joncox123/MotoButtons/ConstructionGuide/Photos/Dremel_PCB_Posts.jpg

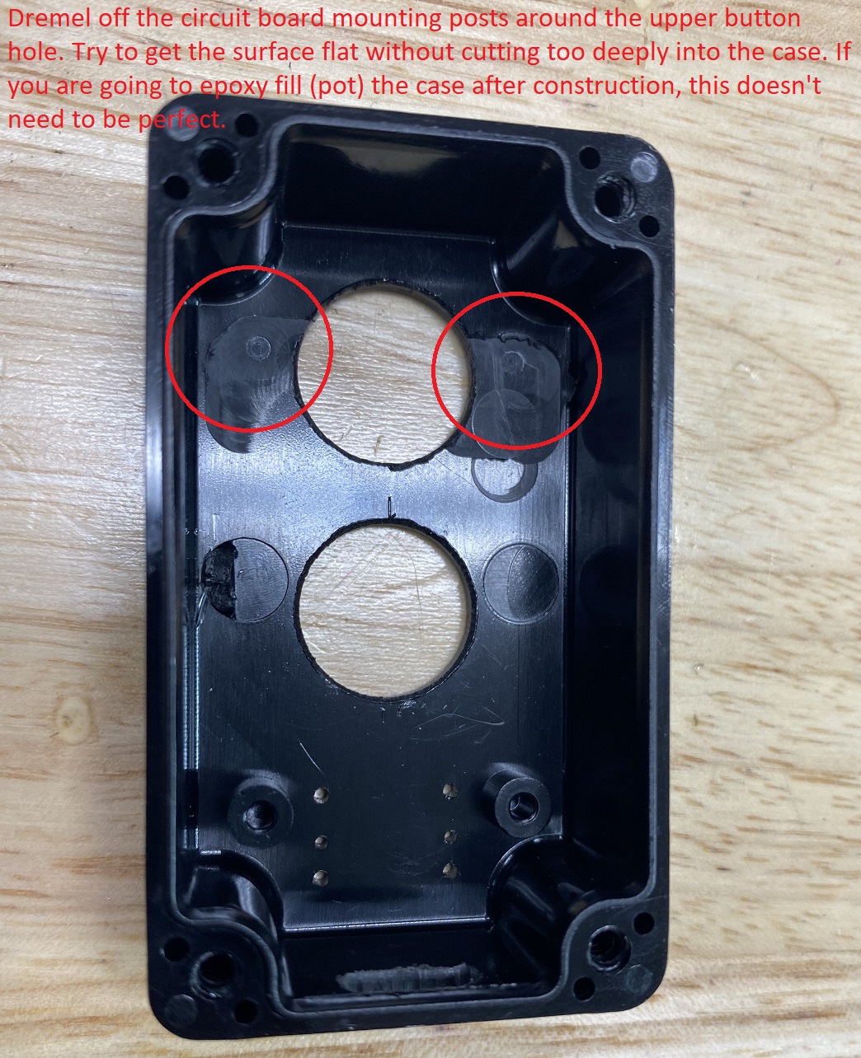
ConstructionGuide/Photos/Dremel_PCB_Posts.jpg
