joncox123/MotoButtons/ConstructionGuide/Photos/seeed-studio-xiao-nrf52840.jpg

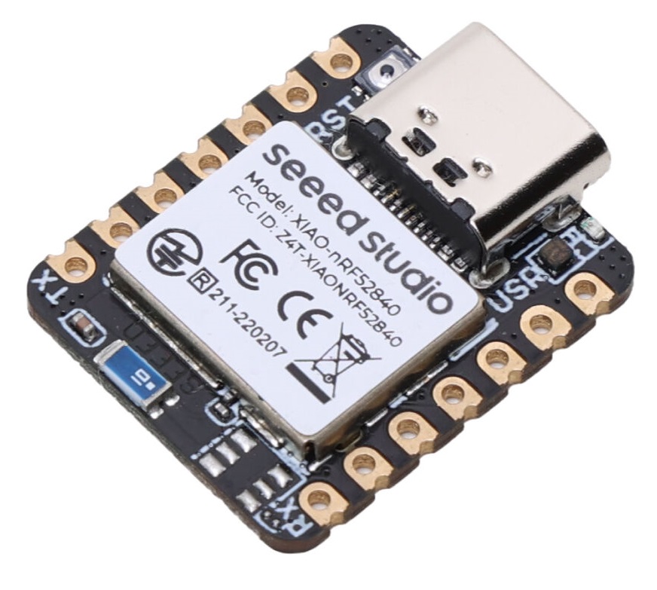
ConstructionGuide/Photos/seeed-studio-xiao-nrf52840.jpg
